anildd-star/RAWF-T/print/stl/07_peg_rail.stl

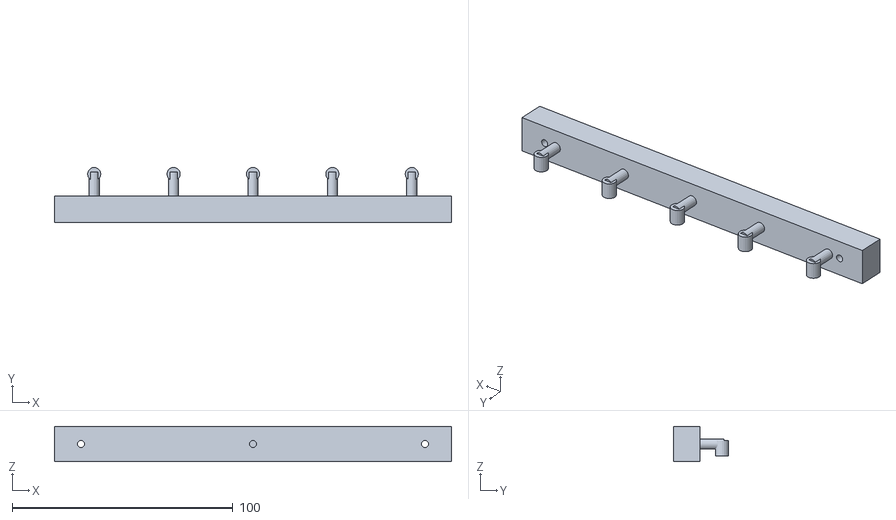
[picture p15: CAD file, 2026-08-08]
print/stl/07_peg_rail.stl
180.0 x 25.0 x 16.0
