anildd-star/RAWF-T/print/stl/06_pistol_mount.stl

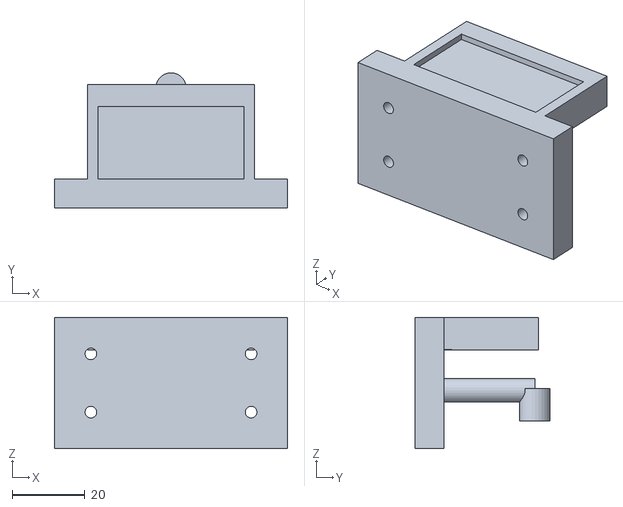
[picture p16: CAD file, 2026-08-08]
print/stl/06_pistol_mount.stl
64.0 x 37.2 x 36.0
