anildd-star/RAWF-T/print/stl/03_rifle_cradle.stl

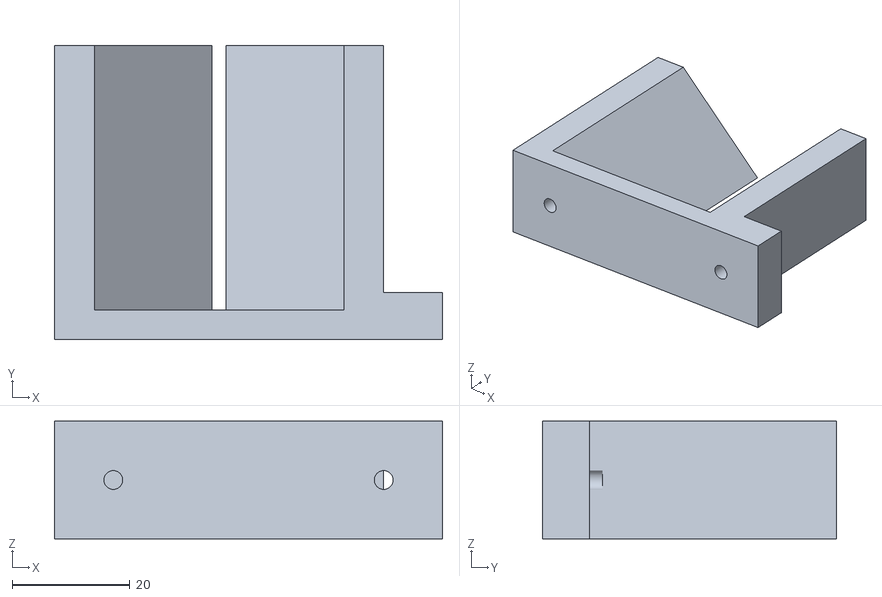
[picture p17: CAD file, 2026-08-08]
print/stl/03_rifle_cradle.stl
66.0 x 50.0 x 20.0
