anildd-star/RAWF-T/print/stl/01_back_panel.stl

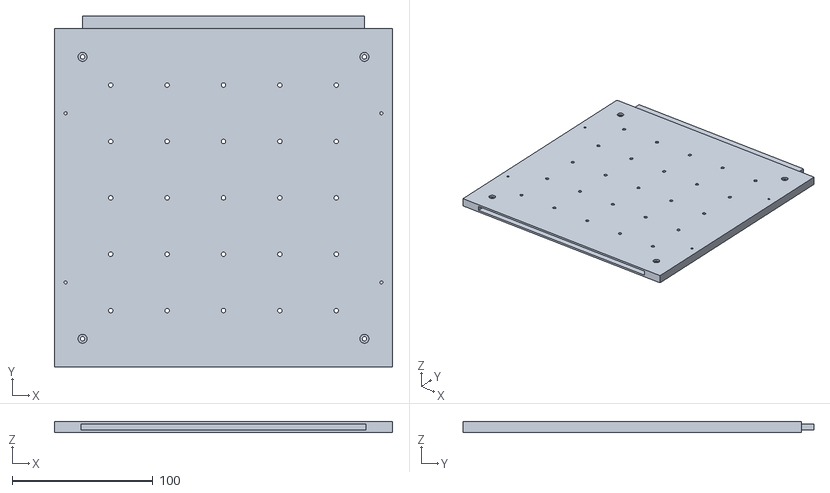
[picture p18: CAD file, 2026-08-08]
print/stl/01_back_panel.stl
240.0 x 249.0 x 8.00
